aotta/RTO-Cart/RTOCart1.1/splash.h

/* C:\Users\Andrea\Documents\Retrocomputer\Intellivision\RTO_Cart\RTOCart1.1\rto.bin (27/01/2023 22:59:48)
   Offset di inizio(h): 00000000, Offset finale(h): 00000BFF, Lunghezza(h): 00000C00 */

unsigned char splash[2560] PROGMEM = {
  0x00, 0x0D, 0x00, 0x50, 0x00, 0x0D, 0x00, 0x50, 0x00, 0x32, 0x00, 0x50,
  0x00, 0x0D, 0x00, 0x50, 0x00, 0x0F, 0x00, 0x50, 0x00, 0x2D, 0x00, 0x50,
  0x03, 0xC0, 0x00, 0x00, 0x00, 0x00, 0x00, 0x01, 0x00, 0x01, 0x00, 0x01,
  0x00, 0x01, 0x00, 0x01, 0x02, 0xBC, 0x02, 0x00, 0x02, 0x44, 0x03, 0x3E,
  0x02, 0xB9, 0x00, 0xF0, 0x01, 0xC0, 0x00, 0x7D, 0x02, 0x0A, 0x00, 0x02,
  0x02, 0x60, 0x02, 0x60, 0x02, 0x09, 0x00, 0x01, 0x02, 0x60, 0x02, 0x04,
  0x00, 0x05, 0x02, 0x60, 0x02, 0x60, 0x02, 0x60, 0x02, 0x60, 0x00, 0x11,
  0x02, 0x2C, 0x00, 0x06, 0x00, 0xAF, 0x00, 0x7B, 0x00, 0x72, 0x00, 0x74,
  0x00, 0x6F, 0x00, 0x00, 0x00, 0x03, 0x02, 0xBE, 0x02, 0xF0, 0x00, 0x04,
  0x01, 0x50, 0x00, 0x14, 0x02, 0xB9, 0x00, 0x0E, 0x02, 0xBC, 0x00, 0xF0,
  0x00, 0x04, 0x01, 0x50, 0x00, 0x1A, 0x02, 0xB9, 0x00, 0xFE, 0x02, 0xBC,
  0x01, 0x00, 0x00, 0x04, 0x01, 0x50, 0x00, 0x1A, 0x01, 0xC0, 0x02, 0xBC,
  0x02, 0xF0, 0x02, 0xB9, 0x00, 0x44, 0x02, 0xE0, 0x02, 0xE0, 0x02, 0xE0,
  0x02, 0xE0, 0x00, 0x11, 0x02, 0x2C, 0x00, 0x06, 0x02, 0x40, 0x01, 0x04,
  0x02, 0xB9, 0x00, 0x58, 0x02, 0xBC, 0x03, 0x08, 0x00, 0x04, 0x01, 0x50,
  0x00, 0x1A, 0x00, 0x04, 0x01, 0x50, 0x03, 0x04, 0x50, 0x61, 0x00, 0x02,
  0x00, 0x17, 0x03, 0x3E, 0x00, 0x08, 0x00, 0x04, 0x01, 0x50, 0x03, 0x04,
  0x50, 0x68, 0x00, 0x17, 0x03, 0x3E, 0x00, 0x08, 0x00, 0x04, 0x01, 0x50,
  0x03, 0x04, 0x50, 0x7F, 0x01, 0xC0, 0x01, 0xE4, 0x02, 0xBA, 0x00, 0x18,
  0x02, 0x60, 0x00, 0x12, 0x02, 0x2C, 0x00, 0x03, 0x02, 0x40, 0x00, 0x30,
  0x02, 0x40, 0x00, 0x31, 0x02, 0xBA, 0xFB, 0xB4, 0x00, 0x0A, 0x02, 0x20,
  0x00, 0x02, 0x03, 0x3E, 0x00, 0x08, 0x00, 0x52, 0x00, 0x52, 0x03, 0xBA,
  0x00, 0x01, 0x02, 0xB9, 0x00, 0x55, 0x02, 0x41, 0x40, 0x40, 0x02, 0xB9,
  0x00, 0xAA, 0x02, 0x41, 0x40, 0x41, 0x02, 0x81, 0x40, 0x40, 0x03, 0x79,
  0x00, 0x55, 0x02, 0x0C, 0x00, 0x08, 0x02, 0x81, 0x40, 0x41, 0x03, 0x79,
  0x00, 0xAA, 0x02, 0x0C, 0x00, 0x02, 0x02, 0xFA, 0x00, 0x02, 0x02, 0x42,
  0x01, 0x03, 0x00, 0x04, 0x01, 0x50, 0x03, 0x04, 0x53, 0x0B, 0x00, 0x04,
  0x01, 0x50, 0x00, 0x14, 0x00, 0x04, 0x01, 0x50, 0x02, 0xF0, 0x00, 0x04,
  0x01, 0x54, 0x00, 0x0B, 0x02, 0xB8, 0x00, 0x02, 0x02, 0x40, 0x01, 0x09,
  0x02, 0xB8, 0x00, 0x38, 0x02, 0x40, 0x01, 0xF8, 0x02, 0x40, 0x00, 0xF8,
  0x00, 0x04, 0x01, 0x50, 0x02, 0xF0, 0x02, 0xB8, 0x00, 0x03, 0x02, 0x40,
  0x01, 0x09, 0x00, 0x04, 0x01, 0x50, 0x02, 0xF0, 0x01, 0xC0, 0x02, 0x40,
  0x01, 0x05, 0x02, 0xB8, 0x00, 0x10, 0x02, 0x40, 0x01, 0x06, 0x02, 0xB8,
  0x51, 0x04, 0x02, 0x40, 0x03, 0x3C, 0x00, 0x04, 0x01, 0x50, 0x02, 0xF0,
  0x02, 0xB8, 0x00, 0x10, 0x02, 0x40, 0x01, 0x05, 0x02, 0x40, 0x01, 0x06,
  0x02, 0xB8, 0x51, 0x44, 0x02, 0x40, 0x03, 0x3C, 0x00, 0x04, 0x01, 0x50,
  0x02, 0xF0, 0x02, 0xB8, 0x00, 0x20, 0x02, 0x40, 0x01, 0x05, 0x02, 0xB8,
  0x00, 0x10, 0x02, 0x40, 0x01, 0x06, 0x02, 0xB8, 0x51, 0x84, 0x02, 0x40,
  0x03, 0x3C, 0x00, 0x04, 0x01, 0x50, 0x02, 0xF0, 0x02, 0xB8, 0x00, 0x30,
  0x02, 0x40, 0x01, 0x05, 0x02, 0xB8, 0x00, 0x0C, 0x02, 0x40, 0x01, 0x06,
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
};
 
